vthahtoan/Nios-II-SoC-FPGA/rtl/wave_cordic.v

module wave_cordic (
    input clk,
    input [31:0] phase_acc,
    output reg [7:0] sin_out,
    output reg [7:0] cos_out
);

    // 1. Phân tích góc phần tư (Quadrant: 00=Q1, 01=Q2, 10=Q3, 11=Q4)
    wire [1:0] quad = phase_acc[31:30];

    // 2. Ép góc về phạm vi 0 đến 90 độ (0 đến 16383)
    // Lật góc nếu đang ở nửa đi xuống (Q2 và Q4) để tạo hình tam giác
    wire [13:0] base_angle = phase_acc[29:16];
    wire [13:0] cordic_angle = (quad == 2'b01 || quad == 2'b11) ? ~base_angle : base_angle;
    wire signed [15:0] target_angle = {2'b00, cordic_angle};

    // 3. Các thanh ghi Pipeline
    reg signed [15:0] x [0:8], y [0:8], z [0:8];
    reg [1:0] quad_delay [0:8];

    always @(posedge clk) begin

        // Tầng 0: Nạp giá trị ban đầu (x đã được thu nhỏ bằng K = 1.64676)
        x[0] <= 16'd9949;
        y[0] <= 16'd0;
        z[0] <= target_angle;
        quad_delay[0] <= quad;

        // Tầng 1: dịch >>> 0 = giữ nguyên
        quad_delay[1] <= quad_delay[0];
        if (z[0] >= 0) begin
            x[1] <= x[0] - (y[0] >>> 0);   // y >>> 0 = y
            y[1] <= y[0] + (x[0] >>> 0);   // x >>> 0 = x
            z[1] <= z[0] - 16'd8192;       // atan(45°)
        end else begin
            x[1] <= x[0] + (y[0] >>> 0);
            y[1] <= y[0] - (x[0] >>> 0);
            z[1] <= z[0] + 16'd8192;
        end

        // Tầng 2: dịch >>> 1 = chia 2
        quad_delay[2] <= quad_delay[1];
        if (z[1] >= 0) begin
            x[2] <= x[1] - (y[1] >>> 1);
            y[2] <= y[1] + (x[1] >>> 1);
            z[2] <= z[1] - 16'd4836;       // atan(26.6°)
        end else begin
            x[2] <= x[1] + (y[1] >>> 1);
            y[2] <= y[1] - (x[1] >>> 1);
            z[2] <= z[1] + 16'd4836;
        end

        // Tầng 3: dịch >>> 2 = chia 4
        quad_delay[3] <= quad_delay[2];
        if (z[2] >= 0) begin
            x[3] <= x[2] - (y[2] >>> 2);
            y[3] <= y[2] + (x[2] >>> 2);
            z[3] <= z[2] - 16'd2555;       // atan(14°)
        end else begin
            x[3] <= x[2] + (y[2] >>> 2);
            y[3] <= y[2] - (x[2] >>> 2);
            z[3] <= z[2] + 16'd2555;
        end

        // Tầng 4: dịch >>> 3 = chia 8
        quad_delay[4] <= quad_delay[3];
        if (z[3] >= 0) begin
            x[4] <= x[3] - (y[3] >>> 3);
            y[4] <= y[3] + (x[3] >>> 3);
            z[4] <= z[3] - 16'd1297;       // atan(7.1°)
        end else begin
            x[4] <= x[3] + (y[3] >>> 3);
            y[4] <= y[3] - (x[3] >>> 3);
            z[4] <= z[3] + 16'd1297;
        end

        // Tầng 5: dịch >>> 4 = chia 16
        quad_delay[5] <= quad_delay[4];
        if (z[4] >= 0) begin
            x[5] <= x[4] - (y[4] >>> 4);
            y[5] <= y[4] + (x[4] >>> 4);
            z[5] <= z[4] - 16'd651;        // atan(3.6°)
        end else begin
            x[5] <= x[4] + (y[4] >>> 4);
            y[5] <= y[4] - (x[4] >>> 4);
            z[5] <= z[4] + 16'd651;
        end

        // Tầng 6: dịch >>> 5 = chia 32
        quad_delay[6] <= quad_delay[5];
        if (z[5] >= 0) begin
            x[6] <= x[5] - (y[5] >>> 5);
            y[6] <= y[5] + (x[5] >>> 5);
            z[6] <= z[5] - 16'd326;        // atan(1.8°)
        end else begin
            x[6] <= x[5] + (y[5] >>> 5);
            y[6] <= y[5] - (x[5] >>> 5);
            z[6] <= z[5] + 16'd326;
        end

        // Tầng 7: dịch >>> 6 = chia 64
        quad_delay[7] <= quad_delay[6];
        if (z[6] >= 0) begin
            x[7] <= x[6] - (y[6] >>> 6);
            y[7] <= y[6] + (x[6] >>> 6);
            z[7] <= z[6] - 16'd163;        // atan(0.9°)
        end else begin
            x[7] <= x[6] + (y[6] >>> 6);
            y[7] <= y[6] - (x[6] >>> 6);
            z[7] <= z[6] + 16'd163;
        end

        // Tầng 8: dịch >>> 7 = chia 128
        quad_delay[8] <= quad_delay[7];
        if (z[7] >= 0) begin
            x[8] <= x[7] - (y[7] >>> 7);
            y[8] <= y[7] + (x[7] >>> 7);
            z[8] <= z[7] - 16'd81;         // atan(0.45°)
        end else begin
            x[8] <= x[7] + (y[7] >>> 7);
            y[8] <= y[7] - (x[7] >>> 7);
            z[8] <= z[7] + 16'd81;
        end

    end

    // 4. Xử lý dấu sau CORDIC (Lật đồ thị theo góc phần tư)
    reg signed [16:0] final_sin, final_cos;
    always @(posedge clk) begin
        case (quad_delay[8])
            2'b00: begin final_sin <=  y[8]; final_cos <=  x[8]; end // Q1: Sin đi lên, Cos dương
            2'b01: begin final_sin <=  y[8]; final_cos <= -x[8]; end // Q2: Sin đi xuống, Cos âm
            2'b10: begin final_sin <= -y[8]; final_cos <= -x[8]; end // Q3: Sin đi xuống âm, Cos âm
            2'b11: begin final_sin <= -y[8]; final_cos <=  x[8]; end // Q4: Sin đi lên âm, Cos dương
        endcase

        // Dời trục để sóng nổi lên trên mức 0 (thành số không dấu 0-255 xuất ra màn hình)
        sin_out <= (final_sin[14:7]) + 8'd128;
        cos_out <= (final_cos[14:7]) + 8'd128;
    end
endmodule
