vthahtoan/Nios-II-SoC-FPGA/rtl/wave_lut.v

module wave_lut(
    input clk,
    input [31:0] phase_acc,
    output reg [7:0] sin_out,
    output reg [7:0] cos_out
);
    (* ramstyle = "block" *) reg [7:0] sin_rom [0:255];
    
    initial begin
        $readmemh("D:/SoC/DoAn/sine.txt", sin_rom);
    end

    reg [7:0] phase_index_sin, phase_index_cos;
    
    always @(posedge clk) begin
        phase_index_sin <= phase_acc[31:24];
        phase_index_cos <= phase_acc[31:24] + 8'd64;
    end
    
    always @(posedge clk) begin
        sin_out <= sin_rom[phase_index_sin];
        cos_out <= sin_rom[phase_index_cos];
    end
endmodule
